Fescron/Project-LabEmbeddedDesign2/documentation/figures/flowchart-2.png

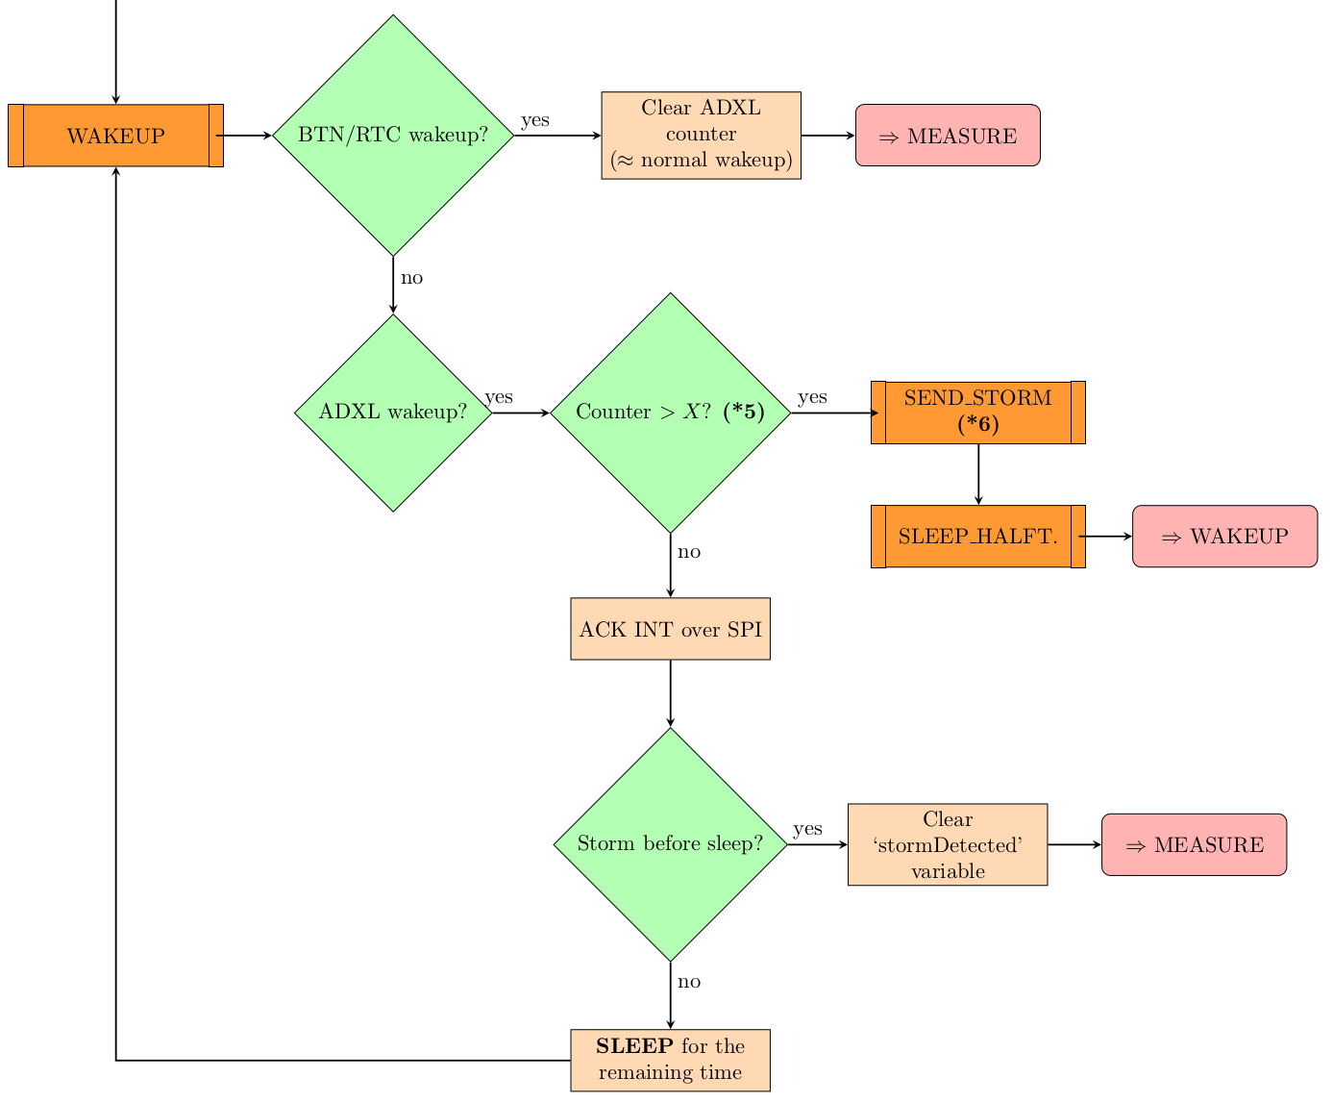
documentation/figures/flowchart-2.png
