Fescron/Project-LabEmbeddedDesign2/documentation/figures/pcb.png

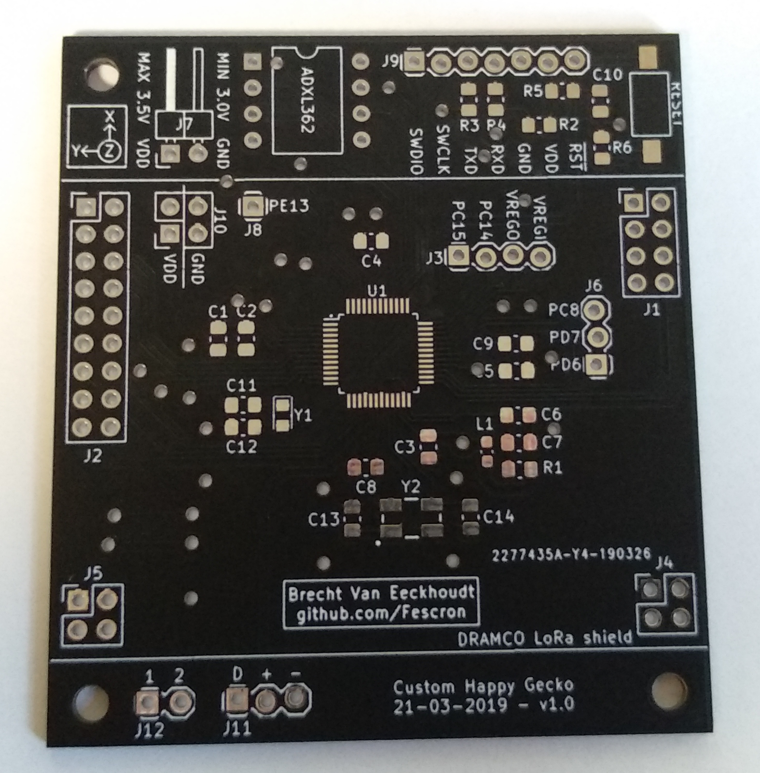
documentation/figures/pcb.png
