Fescron/Project-LabEmbeddedDesign2/documentation/current measurements/measurements-SF/SF07.png

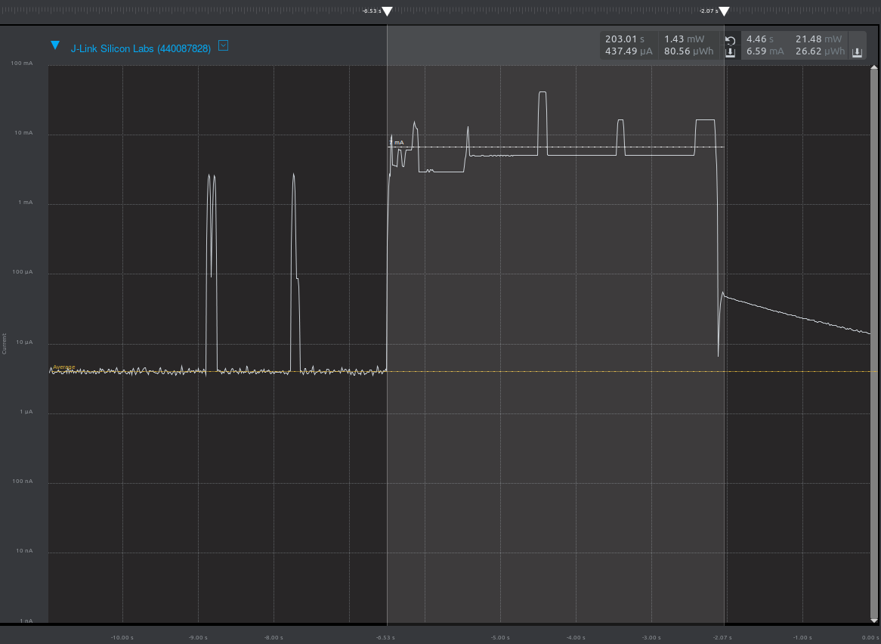
documentation/current measurements/measurements-SF/SF07.png
