Fescron/Project-LabEmbeddedDesign2/documentation/current measurements/measurements-SF/SF08.png

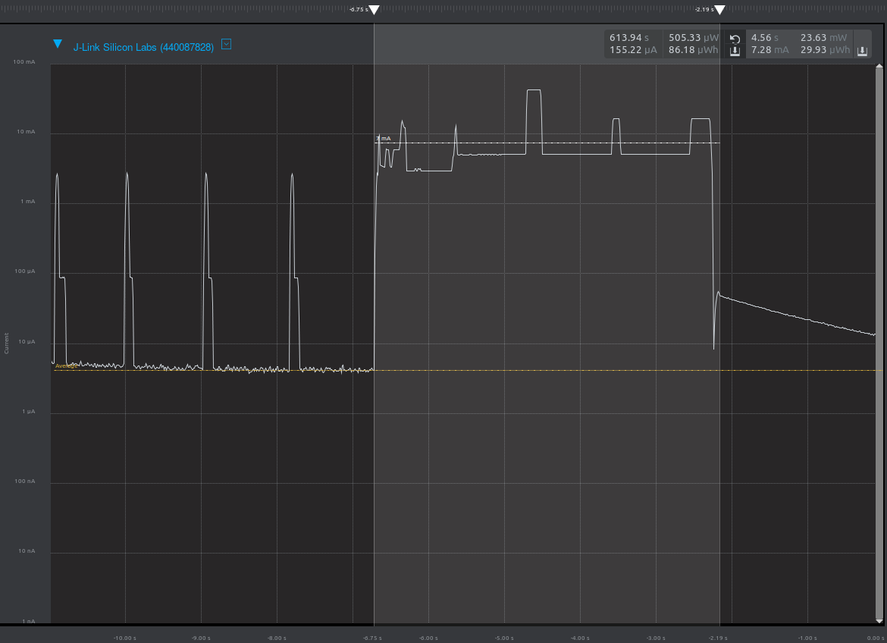
documentation/current measurements/measurements-SF/SF08.png
