Fescron/Project-LabEmbeddedDesign2/documentation/current measurements/measurements-SF/SF11.png

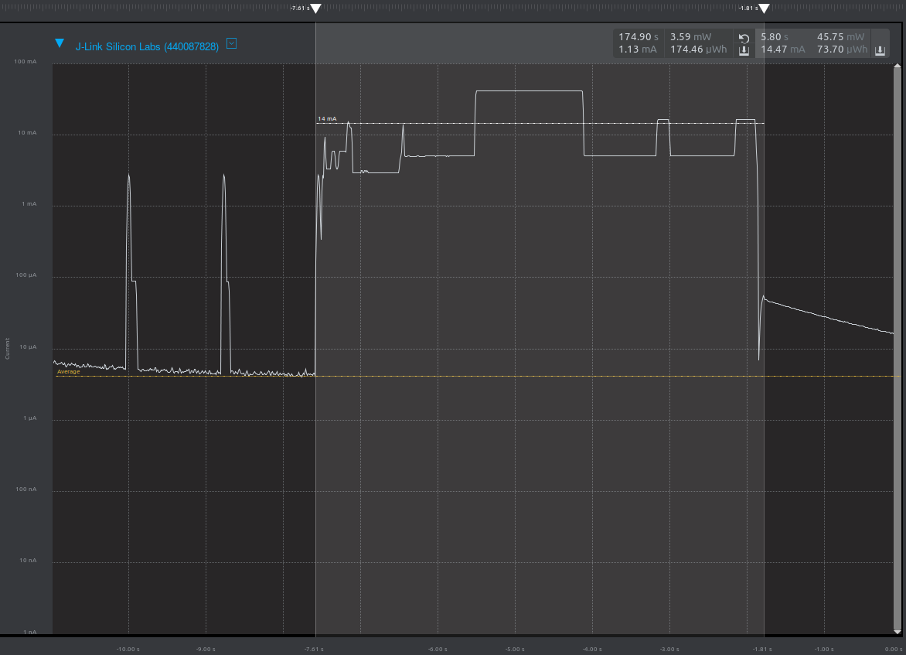
documentation/current measurements/measurements-SF/SF11.png
