Fescron/Project-LabEmbeddedDesign2/documentation/current measurements/measurements-SF/SF12.png

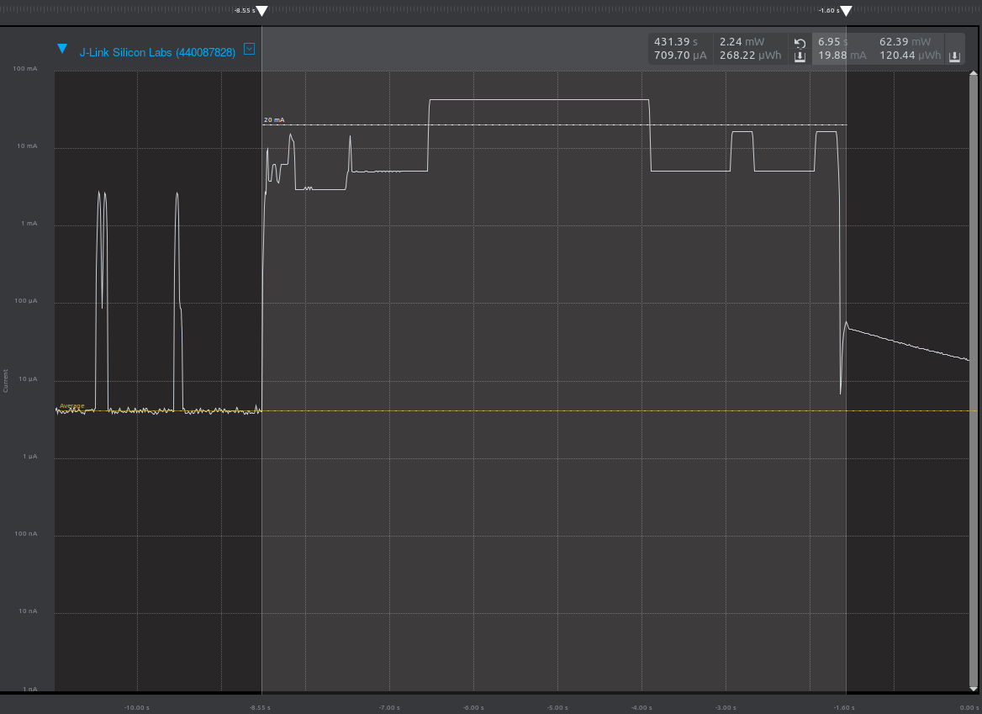
documentation/current measurements/measurements-SF/SF12.png
