Fescron/Project-LabEmbeddedDesign2/hardware/project-embeddedSystemDesign2/pdf/project-embeddedSystemDesign2-F_SilkS.pdf

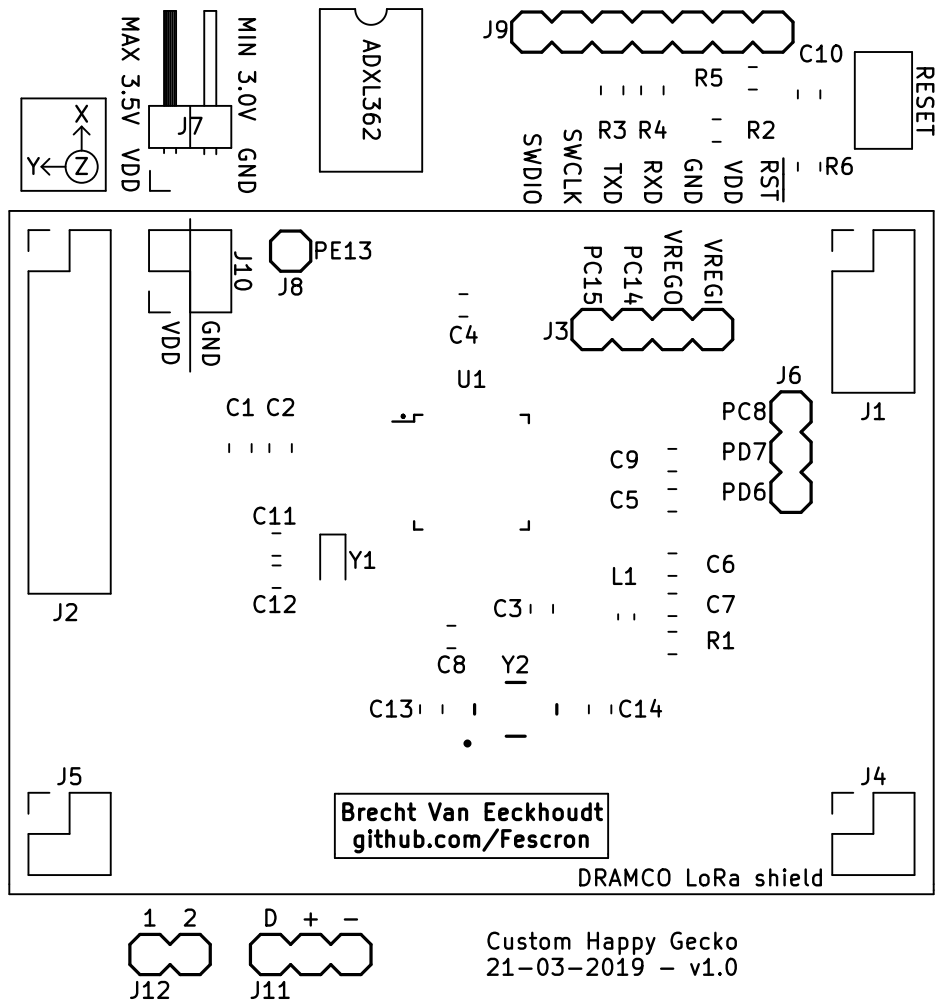
[picture p44: page 1]

21-03-2019 - v1.0 DRAMCO LoRa shield TXD RXD GND VDD RST SWDIO SWCLK
