Fescron/Project-LabEmbeddedDesign2/hardware/project-embeddedSystemDesign2/pdf/project-embeddedSystemDesign2-B_Cu.pdf

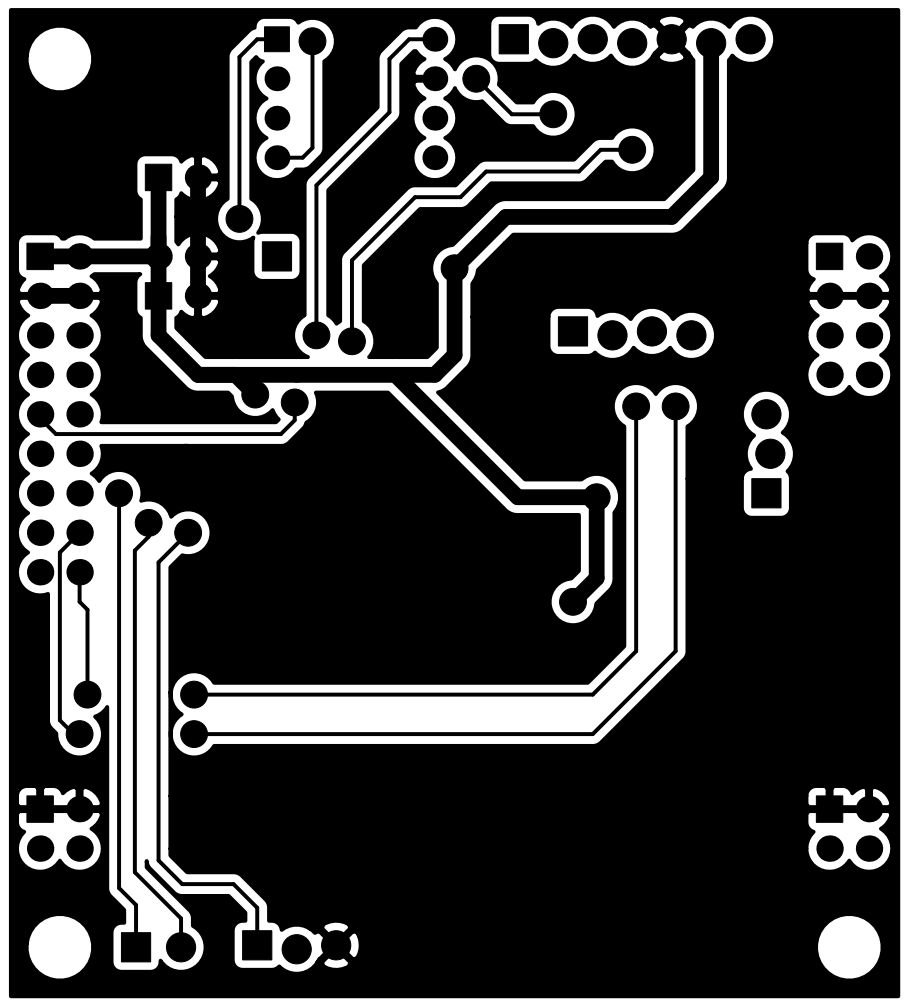
[picture p48: page 1]
