Fescron/Project-LabEmbeddedDesign2/hardware/project-embeddedSystemDesign2/pdf/project-embeddedSystemDesign2-B_Mask-mirrored.pdf

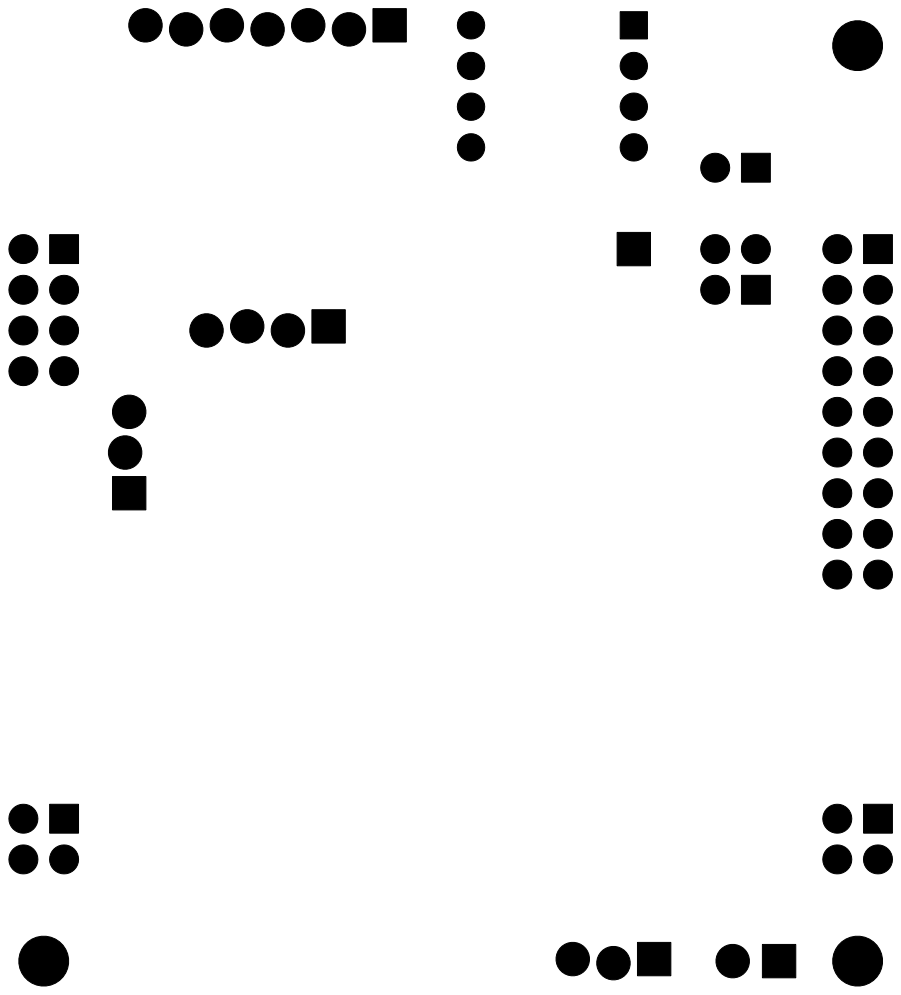
[picture p49: page 1]
