Fescron/Project-LabEmbeddedDesign2/hardware/project-embeddedSystemDesign2/pdf/project-embeddedSystemDesign2-B_Mask.pdf

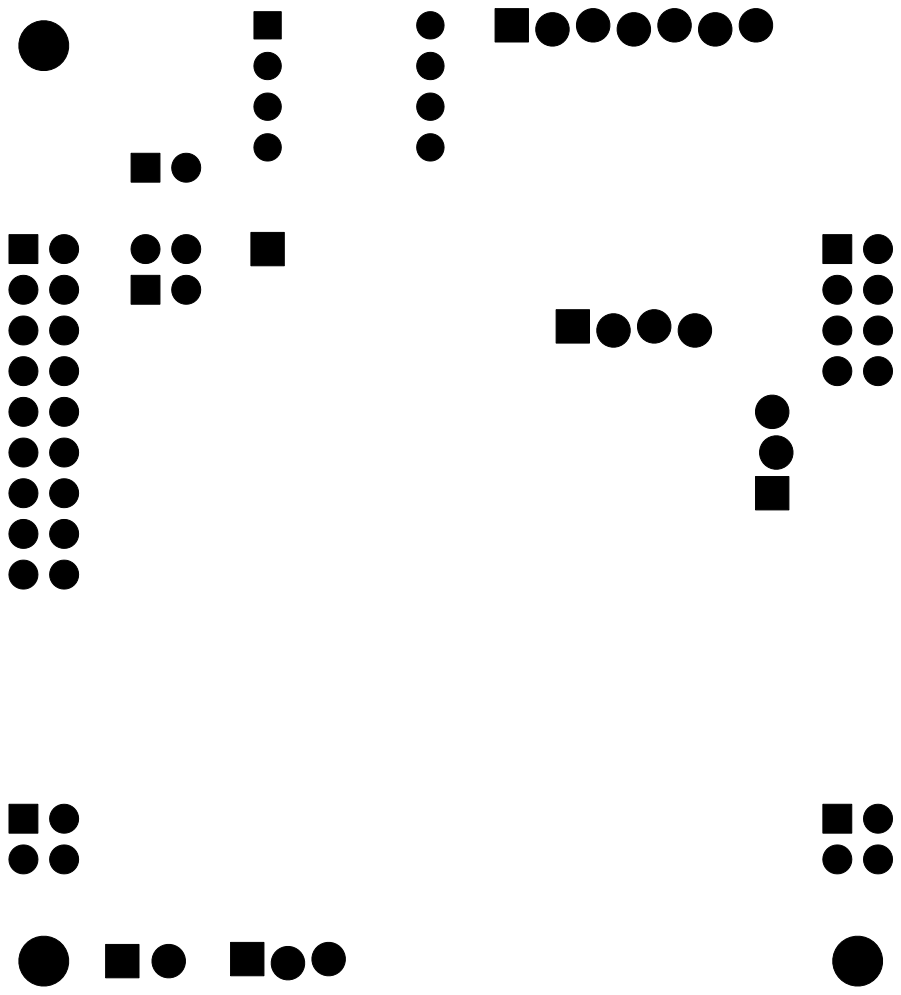
[picture p50: page 1]
