Fescron/Project-LabEmbeddedDesign2/hardware/project-embeddedSystemDesign2/pdf/project-embeddedSystemDesign2-F_Cu.pdf

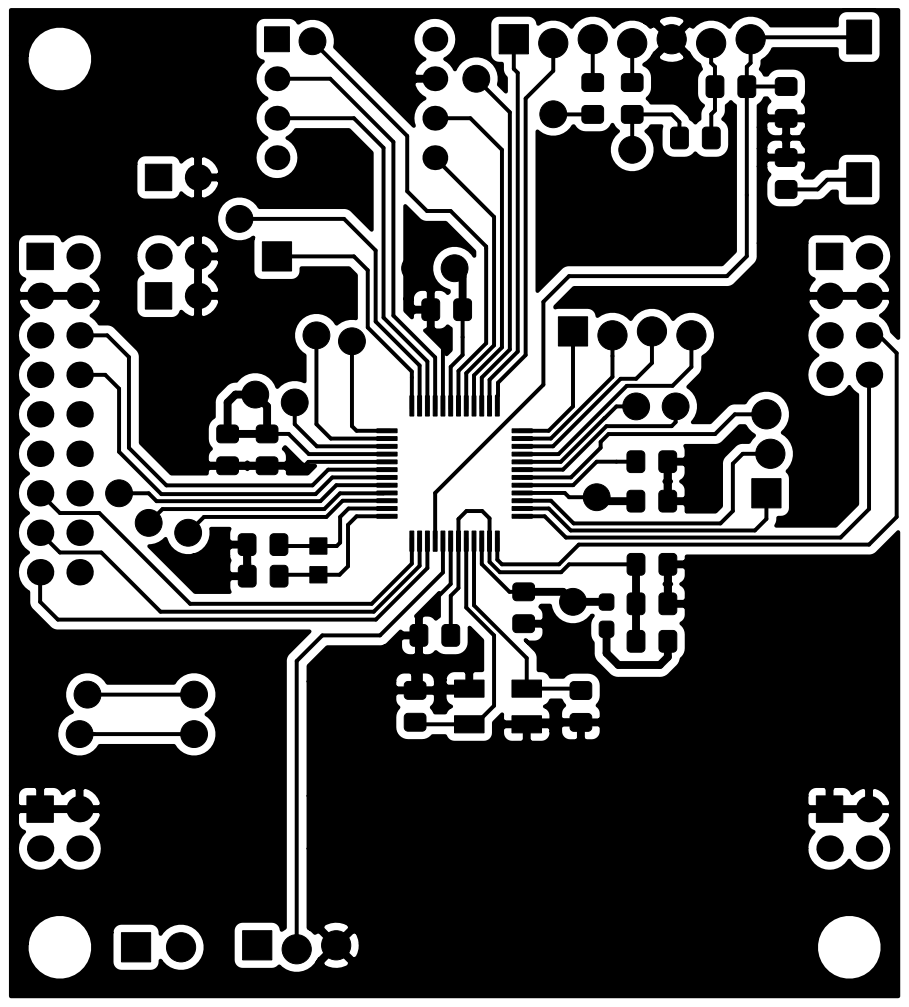
[picture p51: page 1]
